AndreiSaldorfean/AeroGuard/software/poze_website/Gara.jpg

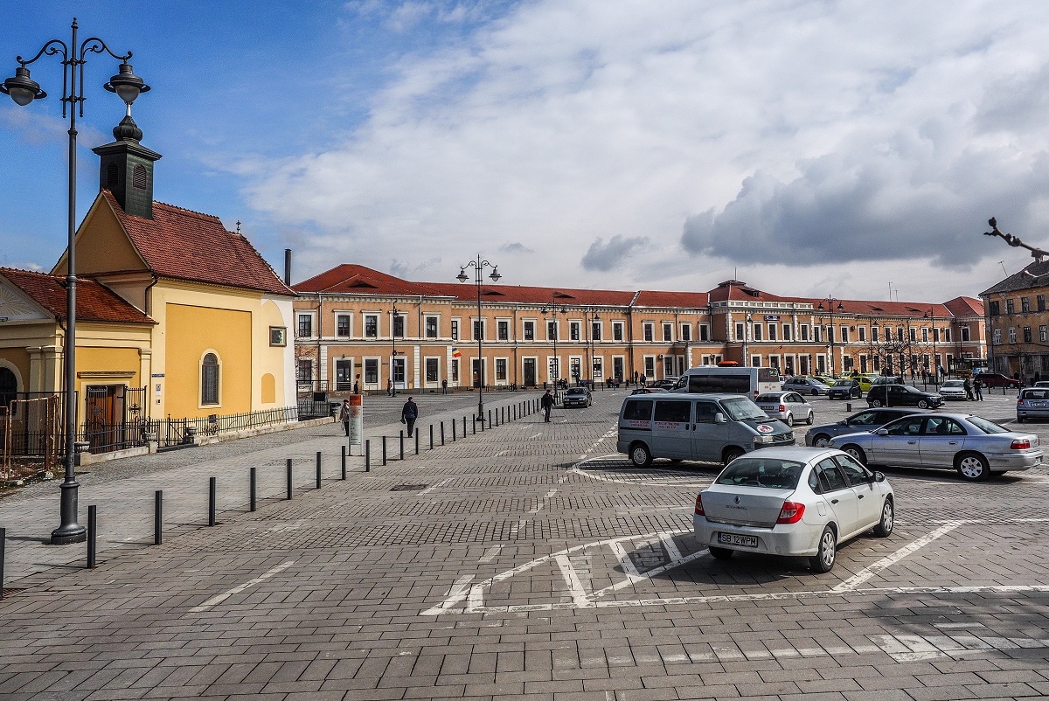
software/poze_website/Gara.jpg
