AndreiSaldorfean/AeroGuard/software/poze_website/Gusterita.jpg

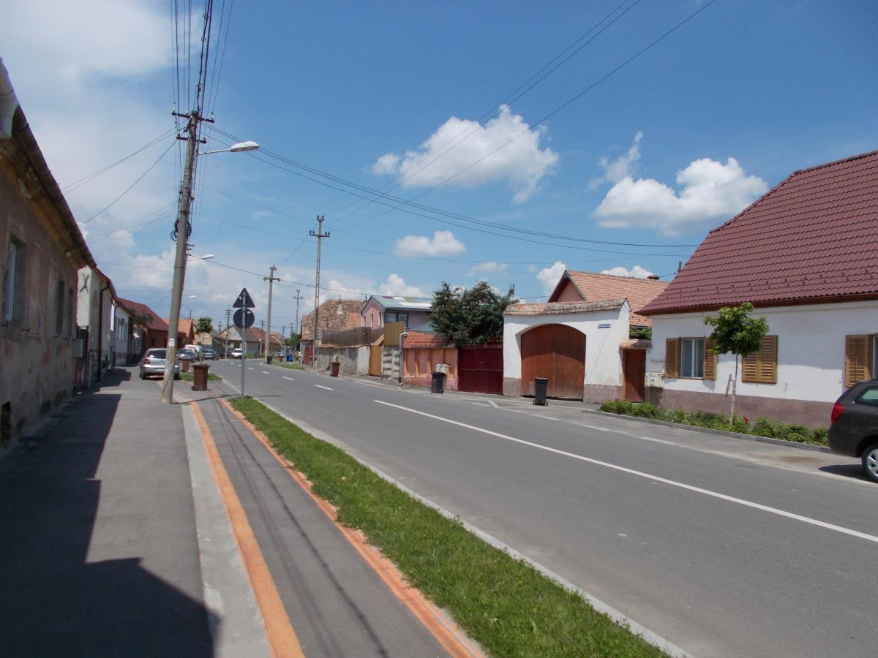
software/poze_website/Gusterita.jpg
