AndreiSaldorfean/AeroGuard/software/poze_website/hipodrom.jpeg

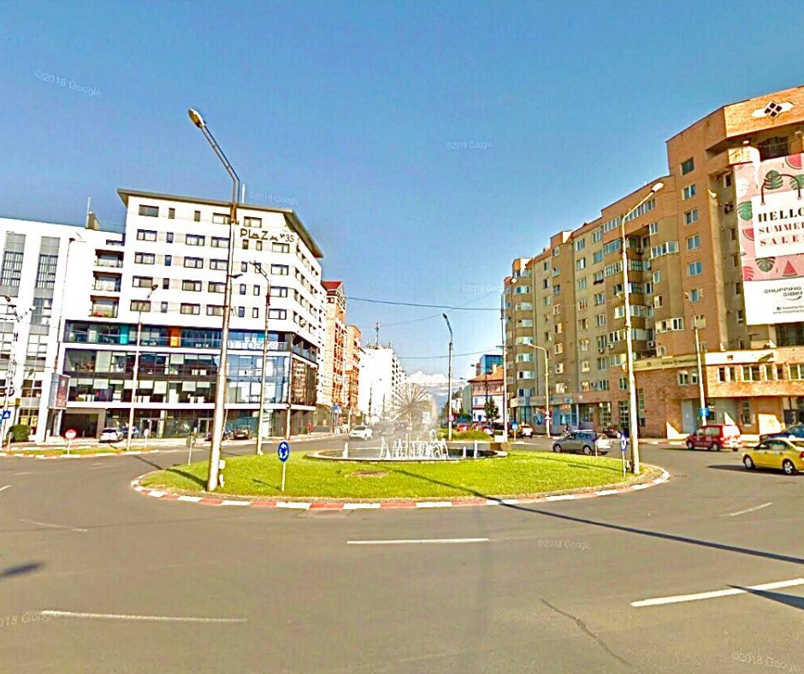
software/poze_website/hipodrom.jpeg
