AndreiSaldorfean/AeroGuard/software/poze_website/Lazaret Sibiu.png

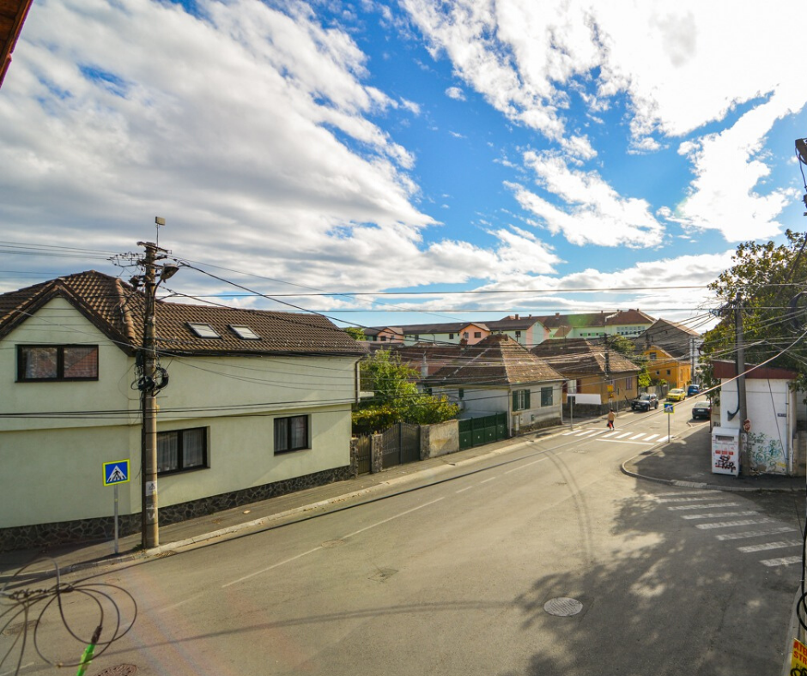
software/poze_website/Lazaret Sibiu.png
