AndreiSaldorfean/AeroGuard/software/poze_website/Orasul De Jos.jpg

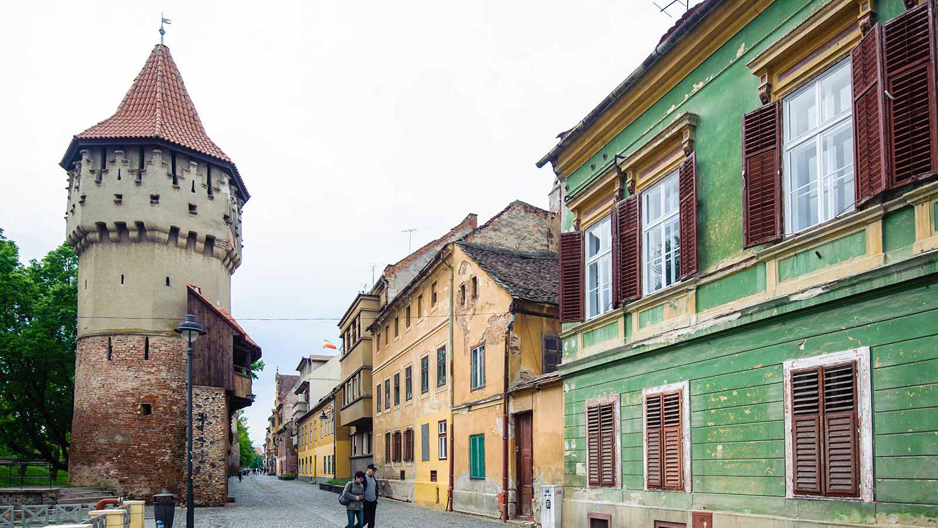
software/poze_website/Orasul De Jos.jpg
