AndreiSaldorfean/AeroGuard/software/poze_website/Strand.jpg

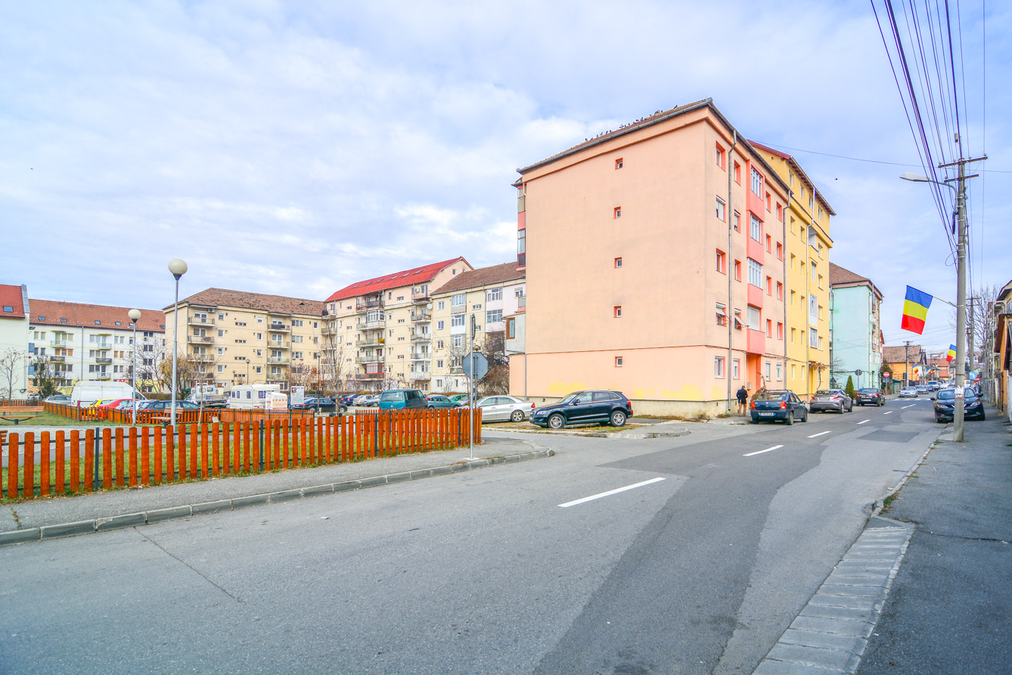
software/poze_website/Strand.jpg
