AndreiSaldorfean/AeroGuard/software/poze_website/Terezian.jpg

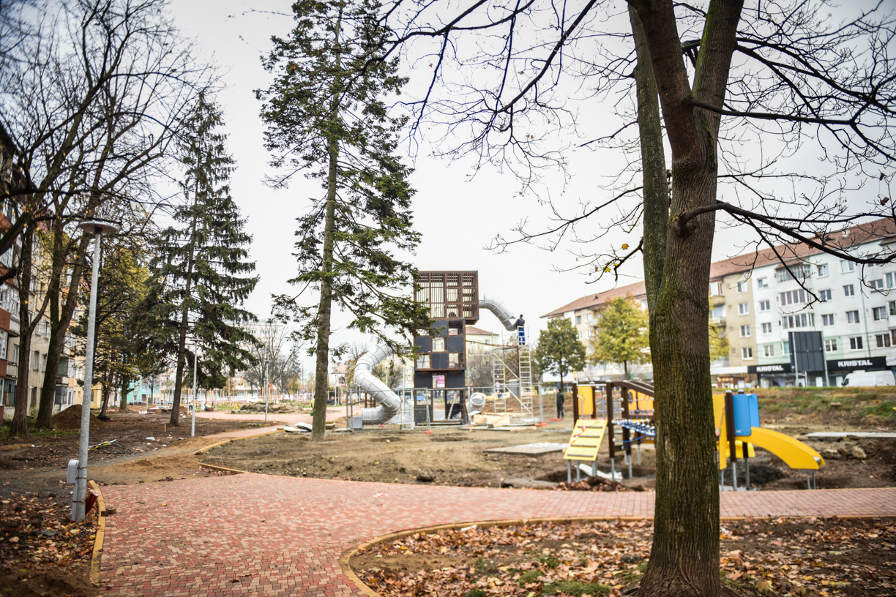
software/poze_website/Terezian.jpg
