AndreiSaldorfean/AeroGuard/software/poze_website/TIglari.jpg

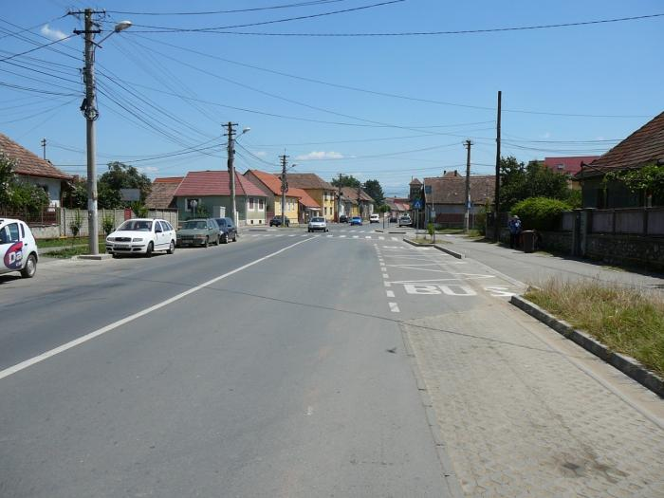
software/poze_website/TIglari.jpg
