AndreiSaldorfean/AeroGuard/software/poze_website/Turnisor.png

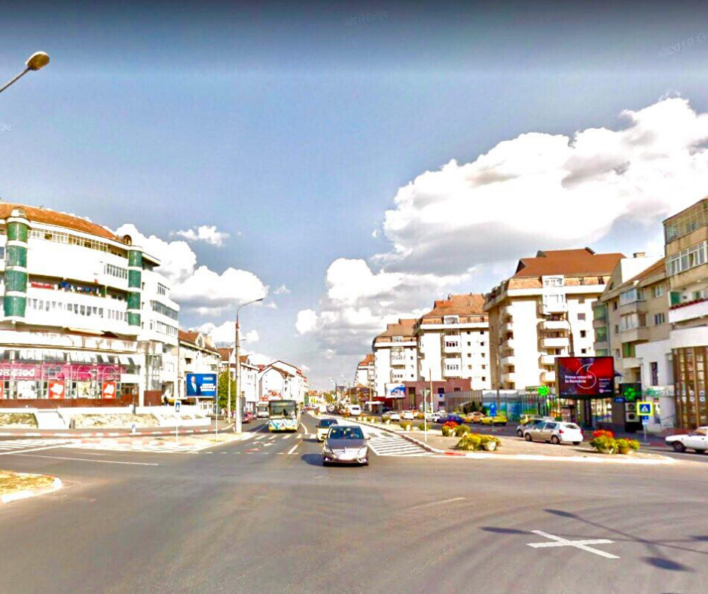
software/poze_website/Turnisor.png
