AndreiSaldorfean/AeroGuard/hardware/eda/montaj_lora.sch

## EAGLE design hardware/eda/montaj_lora.sch (2023-10-03)

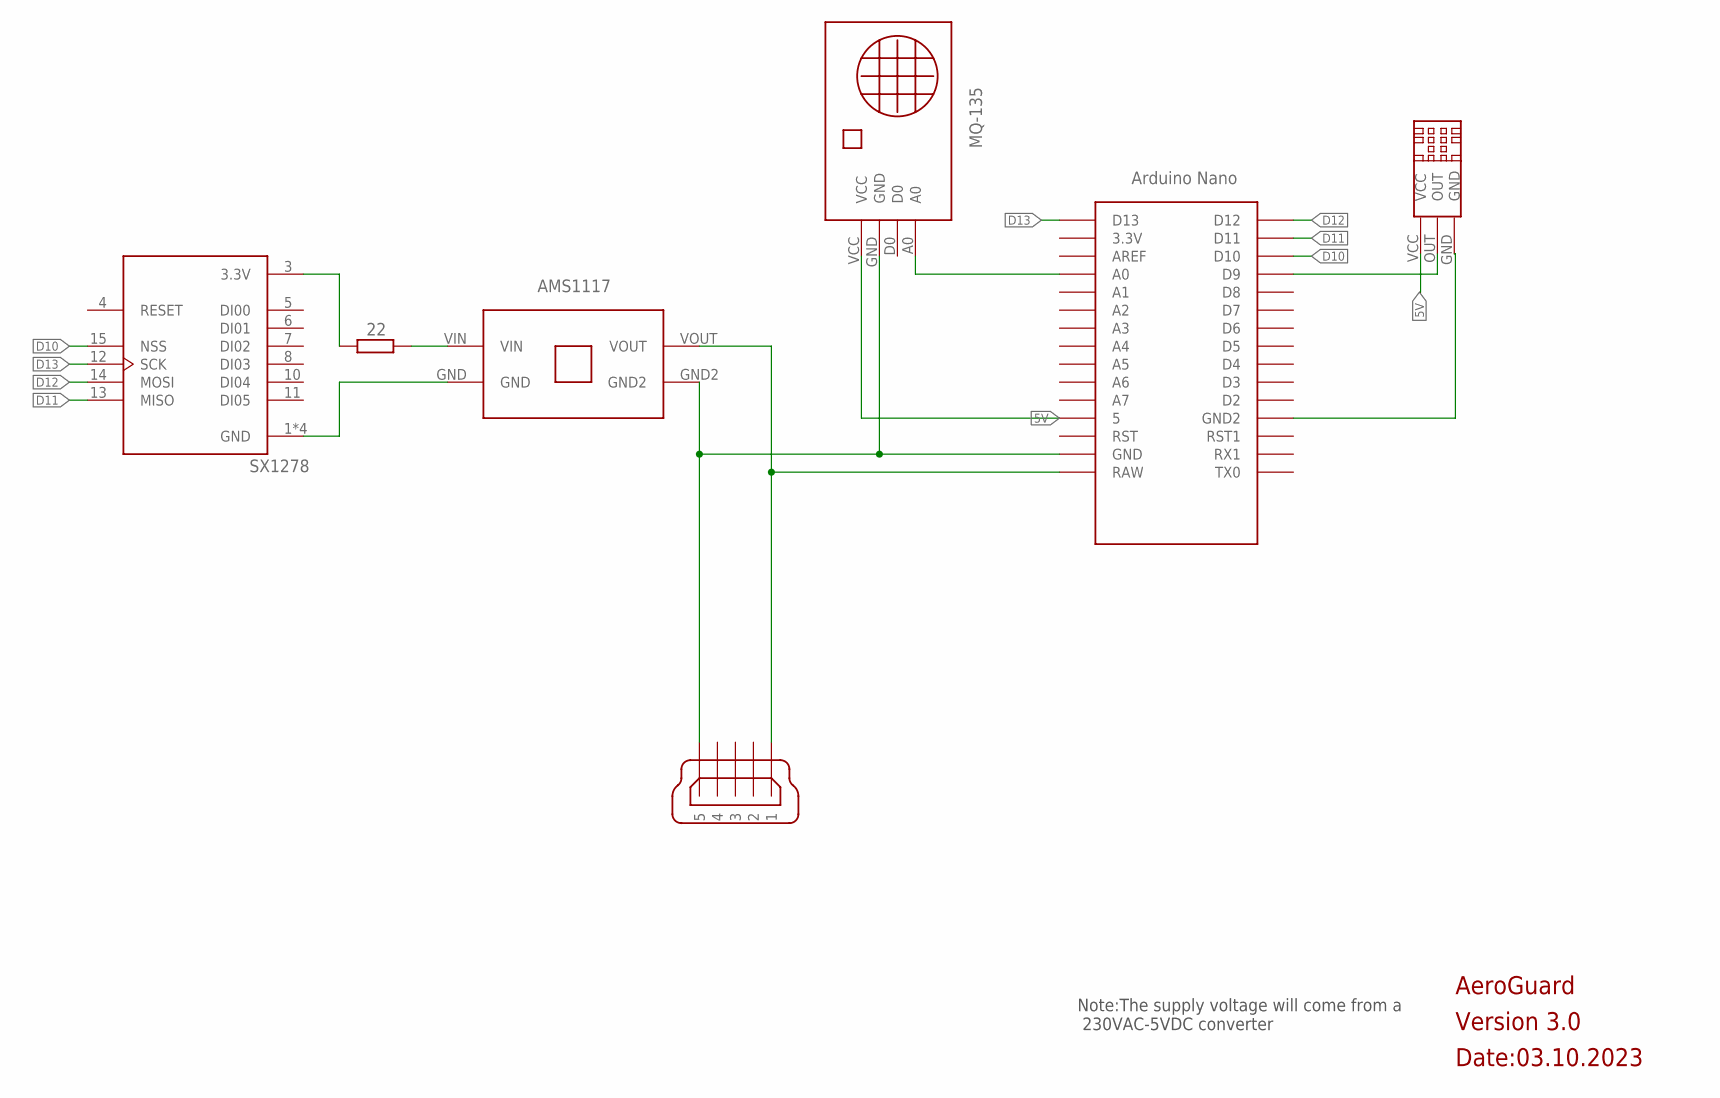
[picture p43: schematic montaj_lora.sch]

Parts:
22: R-EU_0207/12; 0207/12
U1: RA-02_LORA; MODULE_RA-02_LORA
U$1: NANO
U$2: DEV; FOOT
U$3: AMS1117
U$4: DHT11
X1: MINI-USB-SHIELD-UX60-MB-5S8; UX60-MB-5S8

Connections:
5V: U$1.5V (5), U$2.VCC
D10: U1.15 (NSS), U$1.D10
D11: U1.13 (MISO), U$1.D11
D12: U1.14 (MOSI), U$1.D12
D13: U1.12 (SCK), U$1.D13
unnamed: U$1.RAW, U$3.VOUT, X1.1
unnamed: U$1.GND, U$2.GND, U$3.GND2, X1.5
unnamed: 22.2, U$3.VIN
unnamed: 22.1, U1.3 (3.3V)
unnamed: U1.1 (GND), U$3.GND
unnamed: U$1.D9, U$4.OUT
unnamed: U$1.GND1 (GND2), U$4.GND
unnamed: U$1.A0, U$2.A0

Notes on the sheet:
Version 3.0
AeroGuard
Date:03.10.2023
Note:The supply voltage will come from a 230VAC-5VDC converter
SX1278
