AndreiSaldorfean/AeroGuard/hardware/eda/montaj_nrf24l01.sch

## EAGLE design hardware/eda/montaj_nrf24l01.sch (2023-10-03)

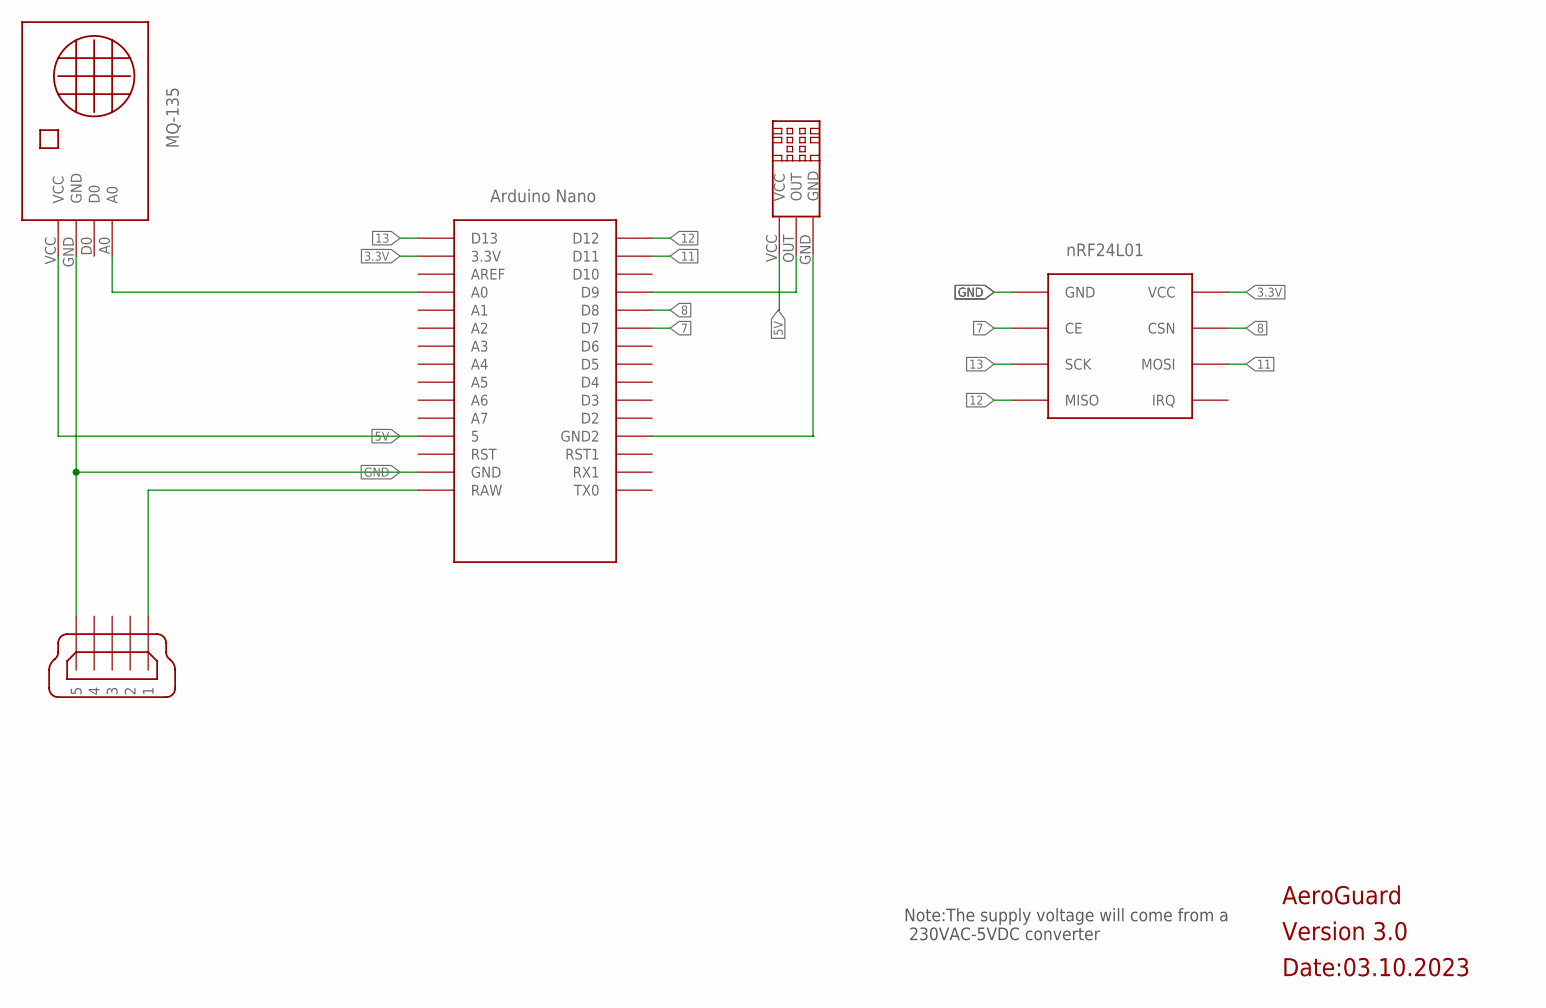
[picture p44: schematic montaj_nrf24l01.sch]

Parts:
GND: NANO
U$1: DHT11
U$2: DEV; FOOT
U$3: NRF24L01
X1: MINI-USB-SHIELD-UX60-MB-5S8; UX60-MB-5S8

Connections:
3.3V: U$3.VCC
5V: GND.5V (5), U$2.VCC
7: U$3.CE
8: U$3.CSN
11: U$3.MOSI
12: U$3.MISO
13: U$3.SCK
GND: U$3.GND
unnamed: GND.A0, U$2.A0
unnamed: GND.D9, U$1.OUT
unnamed: GND.RAW, X1.1
unnamed: GND.GND, U$2.GND, X1.5
unnamed: GND.GND1 (GND2), U$1.GND

Notes on the sheet:
Version 3.0
AeroGuard
Date:03.10.2023
Note:The supply voltage will come from a 230VAC-5VDC converter
